KRuskowski/s5/hw/core/vendor-3d/Crystal_SMD_2016-4Pin_2.0x1.6mm.step

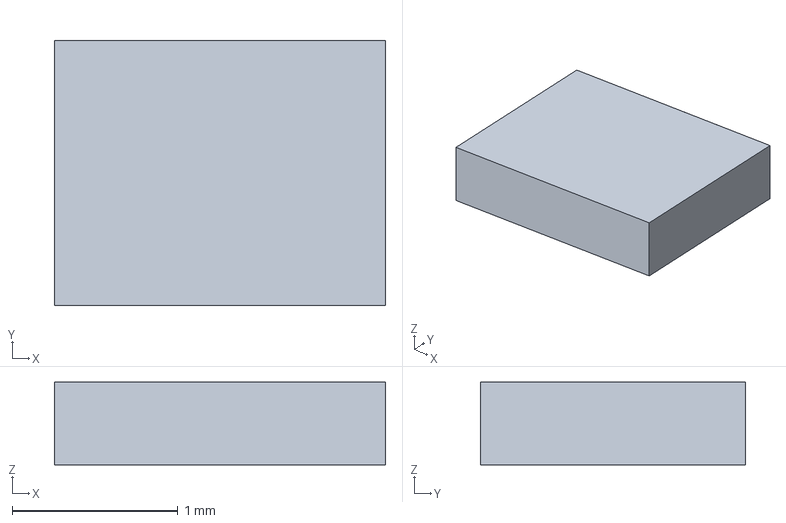
[picture p23: CAD file, 2026-07-04]
hw/core/vendor-3d/Crystal_SMD_2016-4Pin_2.0x1.6mm.step
2.00 x 1.60 x 0.5 mm
