KRuskowski/s5/hw/core/vendor-3d/SW_Push_1P1T_NO_CK_KMR2.step

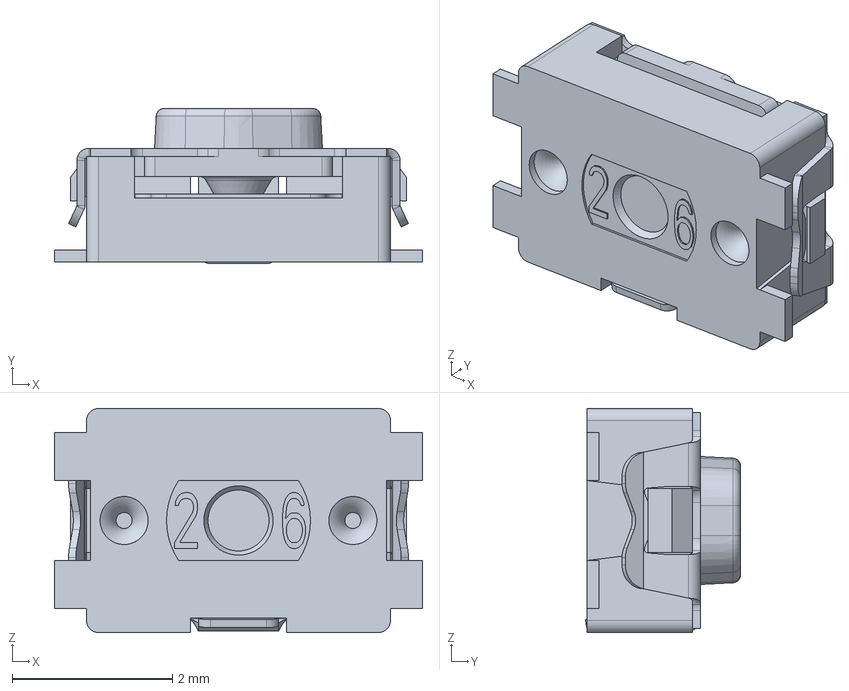
[picture p25: CAD file, 2026-07-04]
hw/core/vendor-3d/SW_Push_1P1T_NO_CK_KMR2.step
4.60 x 1.94 x 2.80 mm
