KRuskowski/s5/hw/power/vendor-3d/Molex_MicroFit_43045-1200_2x06_RA.step

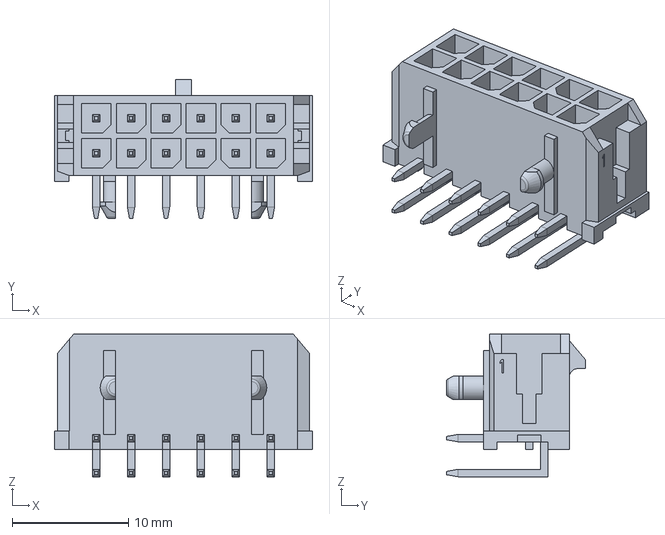
[picture p26: CAD file, 2026-07-07]
hw/power/vendor-3d/Molex_MicroFit_43045-1200_2x06_RA.step
22.1 x 11.9 x 12.2 mm
